meckard10/ZippyWheels/Pi_PicoW_C_Code/writer/bt_setup.cpp

////////////////////////////////////////////////////////////////////////////////

#include <stdio.h>
#include "btstack.h"
#include "pico/cyw43_arch.h"
#include "pico/btstack_cyw43.h"
#include "temp_sensor.h"

#include "bt_setup.h"

////////////////////////////////////////////////////////////////////////////////

#define APP_AD_FLAGS 0x06

////////////////////////////////////////////////////////////////////////////////

btstack_timer_source_t heartbeat;
btstack_packet_callback_registration_t hci_event_callback_registration;

int le_notification_enabled;
hci_con_handle_t con_handle;

void(*global_callback_task)(void);
uint16_t* global_callback_message;

uint8_t adv_data[] = {
    // Flags general discoverable
    0x02, BLUETOOTH_DATA_TYPE_FLAGS, APP_AD_FLAGS,
    // Name
    0x17, BLUETOOTH_DATA_TYPE_COMPLETE_LOCAL_NAME, 'P', 'i', 'c', 'o', ' ', '0', '0', ':', '0', '0', ':', '0', '0', ':', '0', '0', ':', '0', '0', ':', '0', '0',
    0x03, BLUETOOTH_DATA_TYPE_COMPLETE_LIST_OF_16_BIT_SERVICE_CLASS_UUIDS, 0x1a, 0x18,
};
const uint8_t adv_data_len = sizeof(adv_data);

////////////////////////////////////////////////////////////////////////////////

uint16_t att_read_callback(hci_con_handle_t connection_handle, uint16_t att_handle, uint16_t offset, uint8_t * buffer, uint16_t buffer_size);
int att_write_callback(hci_con_handle_t connection_handle, uint16_t att_handle, uint16_t transaction_mode, uint16_t offset, uint8_t *buffer, uint16_t buffer_size);
int bt_init(void(*task)(void), uint16_t& message);
int bt_start();
void heartbeat_handler(struct btstack_timer_source *ts);
void packet_handler(uint8_t packet_type, uint16_t channel, uint8_t *packet, uint16_t size);

////////////////////////////////////////////////////////////////////////////////

uint16_t att_read_callback(hci_con_handle_t connection_handle, uint16_t att_handle, uint16_t offset, uint8_t * buffer, uint16_t buffer_size) {
    UNUSED(connection_handle);

    if (att_handle == ATT_CHARACTERISTIC_ORG_BLUETOOTH_CHARACTERISTIC_TEMPERATURE_01_VALUE_HANDLE){
        return att_read_callback_handle_blob((const uint8_t *)&global_callback_message, sizeof(global_callback_message), offset, buffer, buffer_size);
    }
    return 0;
}

////////////////////////////////////////////////////////////////////////////////

int att_write_callback(hci_con_handle_t connection_handle, uint16_t att_handle, uint16_t transaction_mode, uint16_t offset, uint8_t *buffer, uint16_t buffer_size) {
    UNUSED(transaction_mode);
    UNUSED(offset);
    UNUSED(buffer_size);
    
    if (att_handle != ATT_CHARACTERISTIC_ORG_BLUETOOTH_CHARACTERISTIC_TEMPERATURE_01_CLIENT_CONFIGURATION_HANDLE) return 0;
    le_notification_enabled = little_endian_read_16(buffer, 0) == GATT_CLIENT_CHARACTERISTICS_CONFIGURATION_NOTIFICATION;
    con_handle = connection_handle;
    if (le_notification_enabled) {
        att_server_request_can_send_now_event(con_handle);
    }
    return 0;
}

////////////////////////////////////////////////////////////////////////////////

int bt_init(void(*task)(void), uint16_t* message) {
    global_callback_task = task;
    global_callback_message = message;

    // initialize CYW43 driver architecture (will enable BT if/because CYW43_ENABLE_BLUETOOTH == 1)
    if (cyw43_arch_init()) {
        printf("failed to initialise cyw43_arch\n");
        return -1;
    }

    // Initialize rest of BT Stack
    l2cap_init();
    sm_init();
    att_server_init(profile_data, att_read_callback, att_write_callback);

    // inform about BTstack state
    hci_event_callback_registration.callback = &packet_handler;
    hci_add_event_handler(&hci_event_callback_registration);

    // register for ATT event
    att_server_register_packet_handler(packet_handler);

    // set one-shot btstack timer
    heartbeat.process = &heartbeat_handler;
    btstack_run_loop_set_timer(&heartbeat, HEARTBEAT_PERIOD_MS);
    btstack_run_loop_add_timer(&heartbeat);

    return 0;
}

////////////////////////////////////////////////////////////////////////////////

int bt_start() {
    // turn on bluetooth!
    hci_power_control(HCI_POWER_ON);

    return 0;
}

////////////////////////////////////////////////////////////////////////////////

void heartbeat_handler(struct btstack_timer_source *ts) {
    static uint32_t counter = 0;
    counter++;

    global_callback_task();
    if (le_notification_enabled) {
        att_server_request_can_send_now_event(con_handle);
    }

    // Invert the led
    static int led_on = true;
    led_on = !led_on;
    cyw43_arch_gpio_put(CYW43_WL_GPIO_LED_PIN, led_on);

    // Restart timer
    btstack_run_loop_set_timer(ts, HEARTBEAT_PERIOD_MS);
    btstack_run_loop_add_timer(ts);
}

////////////////////////////////////////////////////////////////////////////////

void packet_handler(uint8_t packet_type, uint16_t channel, uint8_t *packet, uint16_t size) {
    UNUSED(size);
    UNUSED(channel);
    bd_addr_t local_addr;
    if (packet_type != HCI_EVENT_PACKET) return;

    uint8_t event_type = hci_event_packet_get_type(packet);
    switch(event_type){
        case BTSTACK_EVENT_STATE:{
            if (btstack_event_state_get_state(packet) != HCI_STATE_WORKING) return;
            gap_local_bd_addr(local_addr);
            printf("BTstack up and running on %s.\n", bd_addr_to_str(local_addr));

            // setup advertisements
            uint16_t adv_int_min = 800;
            uint16_t adv_int_max = 800;
            uint8_t adv_type = 0;
            bd_addr_t null_addr;
            memset(null_addr, 0, 6);
            gap_advertisements_set_params(adv_int_min, adv_int_max, adv_type, 0, null_addr, 0x07, 0x00);
            assert(adv_data_len <= 31); // ble limitation
            gap_advertisements_set_data(adv_data_len, (uint8_t*) adv_data);
            gap_advertisements_enable(1);

            global_callback_task();

            break;}
        case HCI_EVENT_DISCONNECTION_COMPLETE:
            le_notification_enabled = 0;
            break;
        case ATT_EVENT_CAN_SEND_NOW:
            att_server_notify(con_handle, ATT_CHARACTERISTIC_ORG_BLUETOOTH_CHARACTERISTIC_TEMPERATURE_01_VALUE_HANDLE, (uint8_t*)global_callback_message, sizeof(global_callback_message));
            printf("wrote %d\n", *global_callback_message);
            break;
        default:
            break;
    }
}
